santicastro/ArduinoDartBoard/_init.ino

void setupButtonMatrix(){

  button btn118 = {
    1, DOUBLE_BUTTON  };
  buttons[118] = btn118;

  button btn117 = {
    1, EXTERNAL_BUTTON  };
  buttons[117] = btn117;

  button btn119 = {
    1, TRIPLE_BUTTON  };
  buttons[119] = btn119;

  button btn120 = {
    1, INTERNAL_BUTTON  };
  buttons[120] = btn120;

  button btn54 = {
    2, DOUBLE_BUTTON  };
  buttons[54] = btn54;

  button btn53 = {
    2, EXTERNAL_BUTTON  };
  buttons[53] = btn53;

  button btn55 = {
    2, TRIPLE_BUTTON  };
  buttons[55] = btn55;

  button btn56 = {
    2, INTERNAL_BUTTON  };
  buttons[56] = btn56;

  button btn86 = {
    3, DOUBLE_BUTTON  };
  buttons[86] = btn86;

  button btn85 = {
    3, EXTERNAL_BUTTON  };
  buttons[85] = btn85;

  button btn87 = {
    3, TRIPLE_BUTTON  };
  buttons[87] = btn87;

  button btn88 = {
    3, INTERNAL_BUTTON  };
  buttons[88] = btn88;

  button btn150 = {
    4, DOUBLE_BUTTON  };
  buttons[150] = btn150;

  button btn149 = {
    4, EXTERNAL_BUTTON  };
  buttons[149] = btn149;

  button btn151 = {
    4, TRIPLE_BUTTON  };
  buttons[151] = btn151;

  button btn152 = {
    4, INTERNAL_BUTTON  };
  buttons[152] = btn152;

  button btn131 = {
    5, DOUBLE_BUTTON  };
  buttons[131] = btn131;

  button btn130 = {
    5, EXTERNAL_BUTTON  };
  buttons[130] = btn130;

  button btn129 = {
    5, TRIPLE_BUTTON  };
  buttons[129] = btn129;

  button btn137 = {
    5, INTERNAL_BUTTON  };
  buttons[137] = btn137;

  button btn6 = {
    6, DOUBLE_BUTTON  };
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

  button btn113 = {
    20, TRIPLE_BUTTON  };
  buttons[113] = btn113;

  button btn121 = {
    20, INTERNAL_BUTTON  };
  buttons[121] =  btn121;

  button btn132 = {
    25, NORMAL_BUTTON  };
  buttons[132] =  btn132;

  button btn116 = {
    25, DOUBLE_BUTTON  };
  buttons[116] =  btn116;
}
